tanjeffreyz/electrotactile-braille-display/images/oscilloscope_readings/IMG_0008.JPG

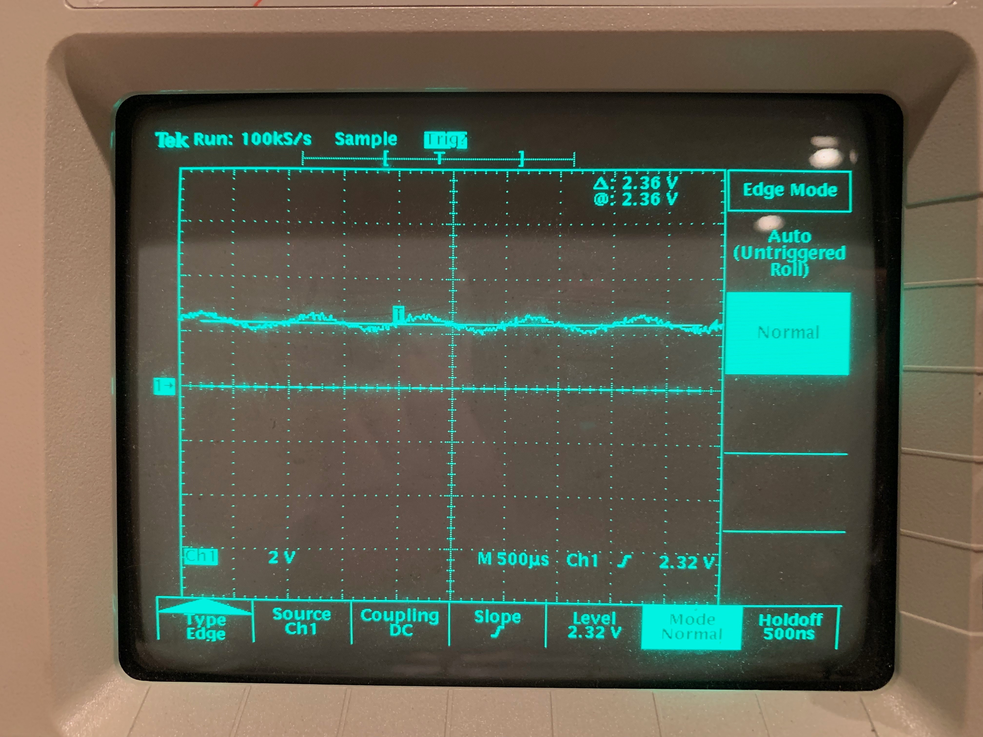
images/oscilloscope_readings/IMG_0008.JPG
