tanjeffreyz/electrotactile-braille-display/images/oscilloscope_readings/IMG_0009.JPG

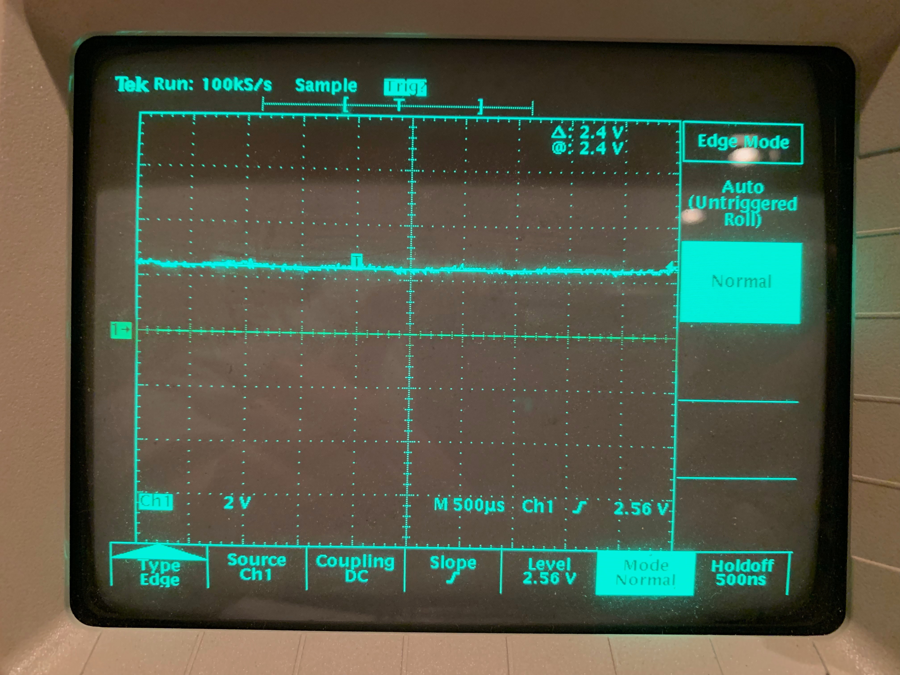
images/oscilloscope_readings/IMG_0009.JPG
