tanjeffreyz/electrotactile-braille-display/images/oscilloscope_readings/IMG_0010.JPG

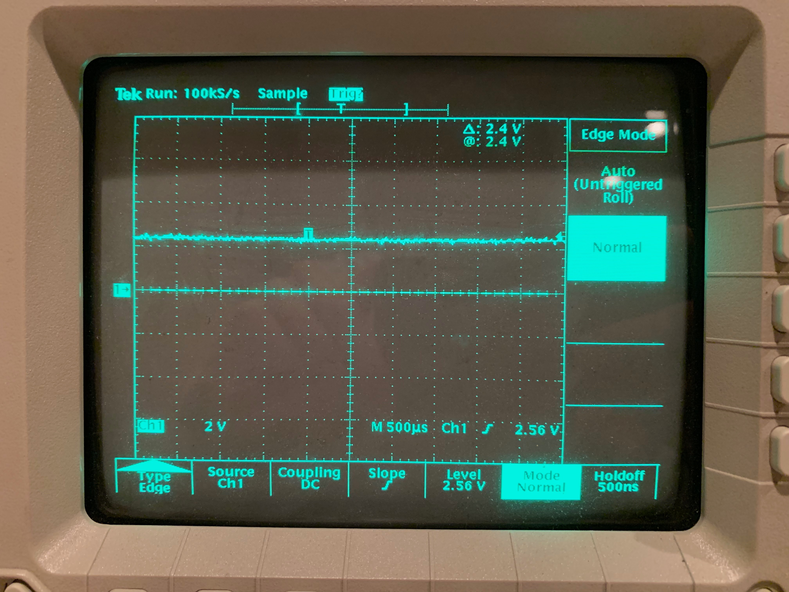
images/oscilloscope_readings/IMG_0010.JPG
