tanjeffreyz/electrotactile-braille-display/images/oscilloscope_readings/IMG_0014.JPG

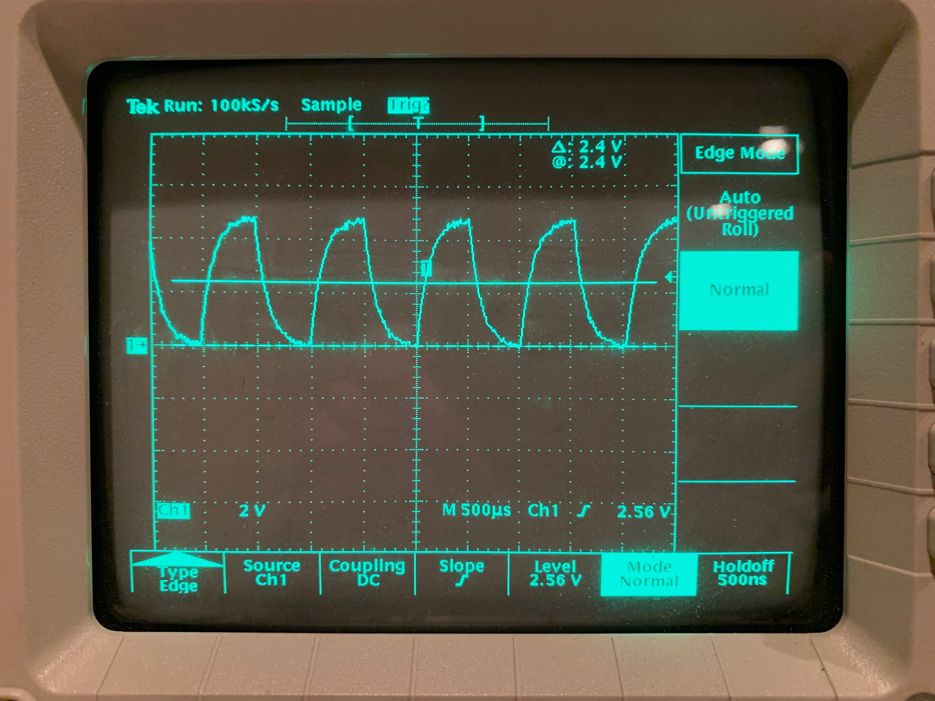
images/oscilloscope_readings/IMG_0014.JPG
