tanjeffreyz/electrotactile-braille-display/images/oscilloscope_readings/IMG_0118.JPG

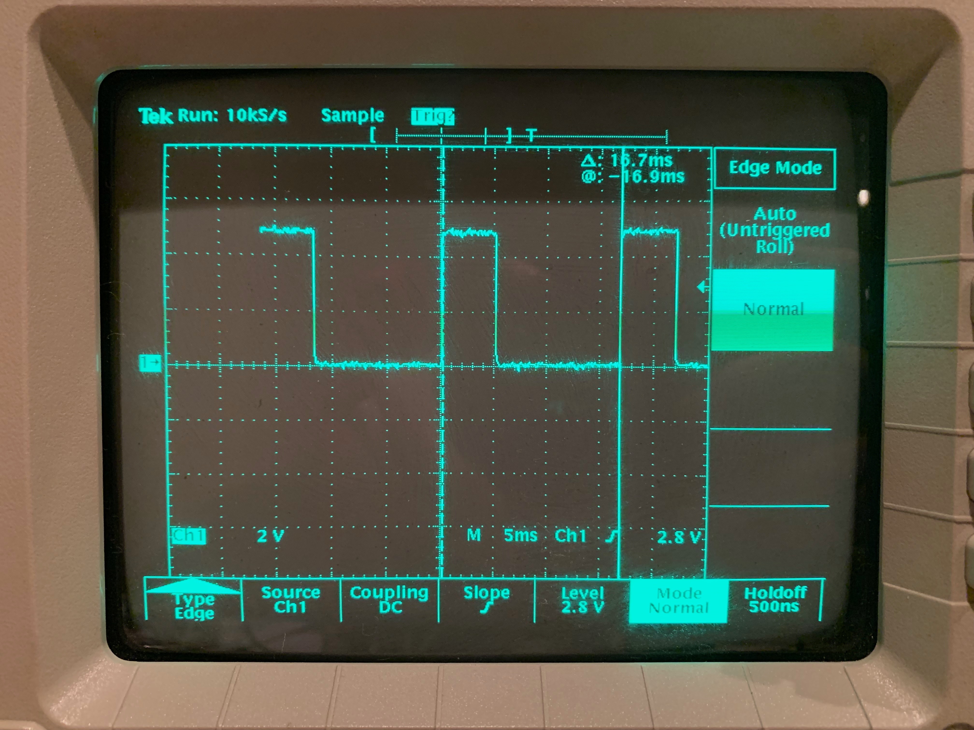
images/oscilloscope_readings/IMG_0118.JPG
