tanjeffreyz/electrotactile-braille-display/images/oscilloscope_readings/IMG_0120.JPG

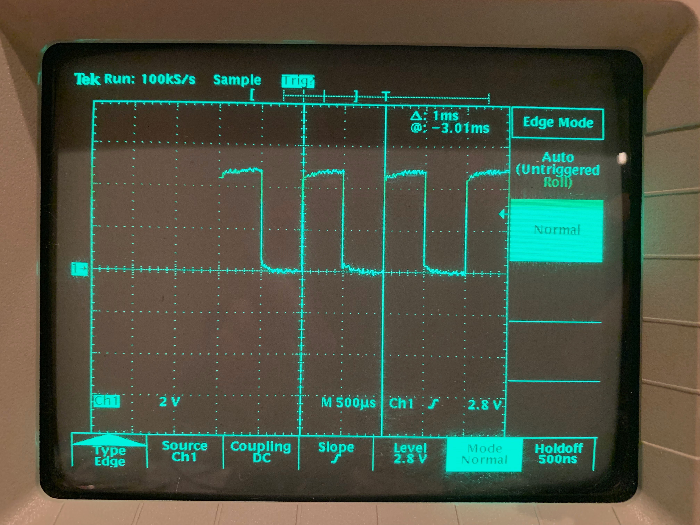
images/oscilloscope_readings/IMG_0120.JPG
