tanjeffreyz/electrotactile-braille-display/images/oscilloscope_readings/IMG_0123.JPG

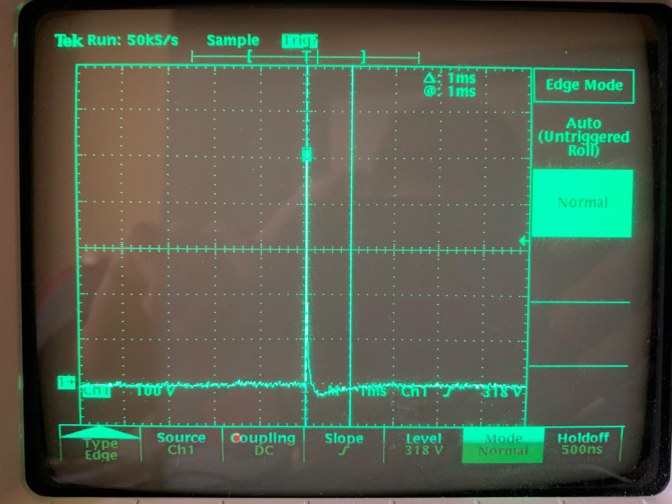
images/oscilloscope_readings/IMG_0123.JPG
