tanjeffreyz/electrotactile-braille-display/images/oscilloscope_readings/IMG_0124.JPG

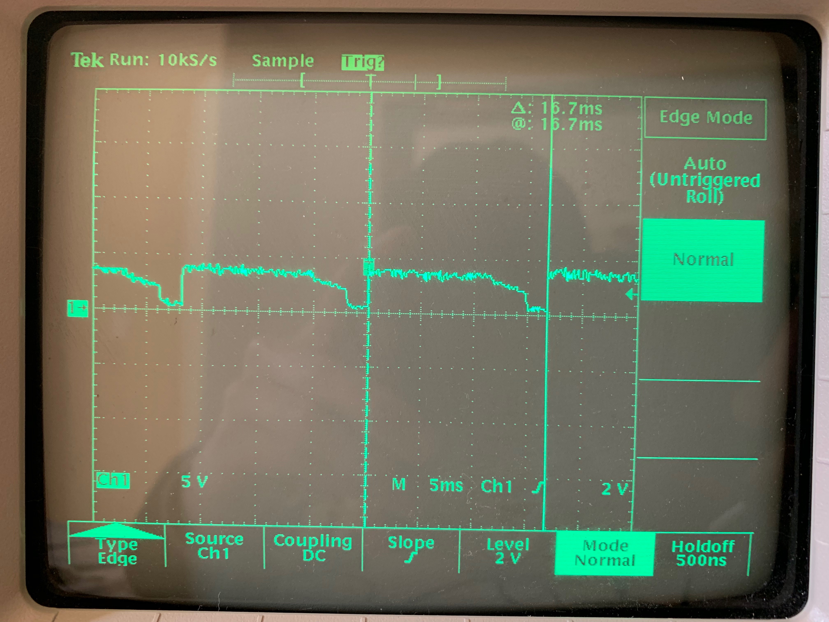
images/oscilloscope_readings/IMG_0124.JPG
