tanjeffreyz/electrotactile-braille-display/images/oscilloscope_readings/IMG_0125.JPG

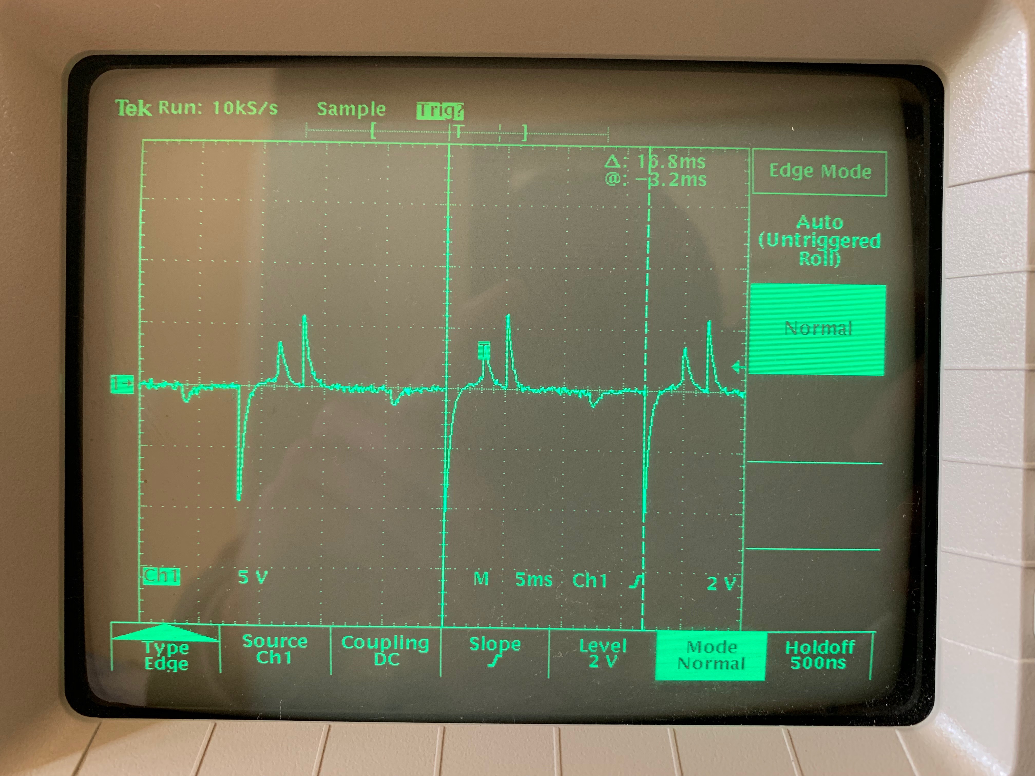
images/oscilloscope_readings/IMG_0125.JPG
