tanjeffreyz/electrotactile-braille-display/images/oscilloscope_readings/IMG_0386.JPG

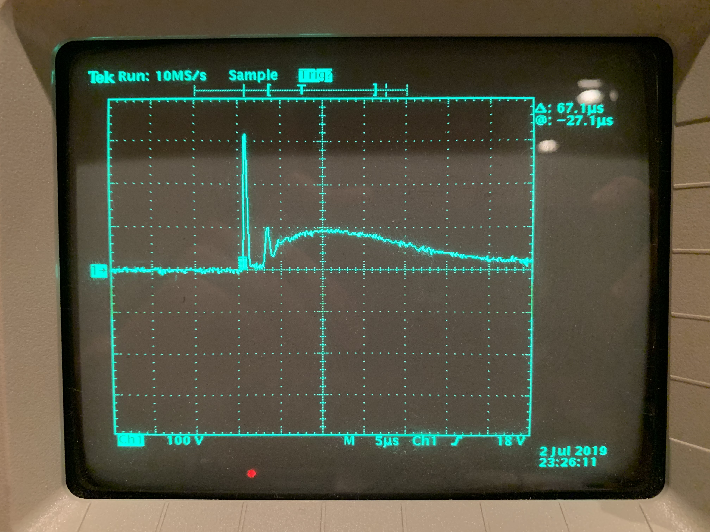
images/oscilloscope_readings/IMG_0386.JPG
