tanjeffreyz/electrotactile-braille-display/images/oscilloscope_readings/IMG_0387.JPG

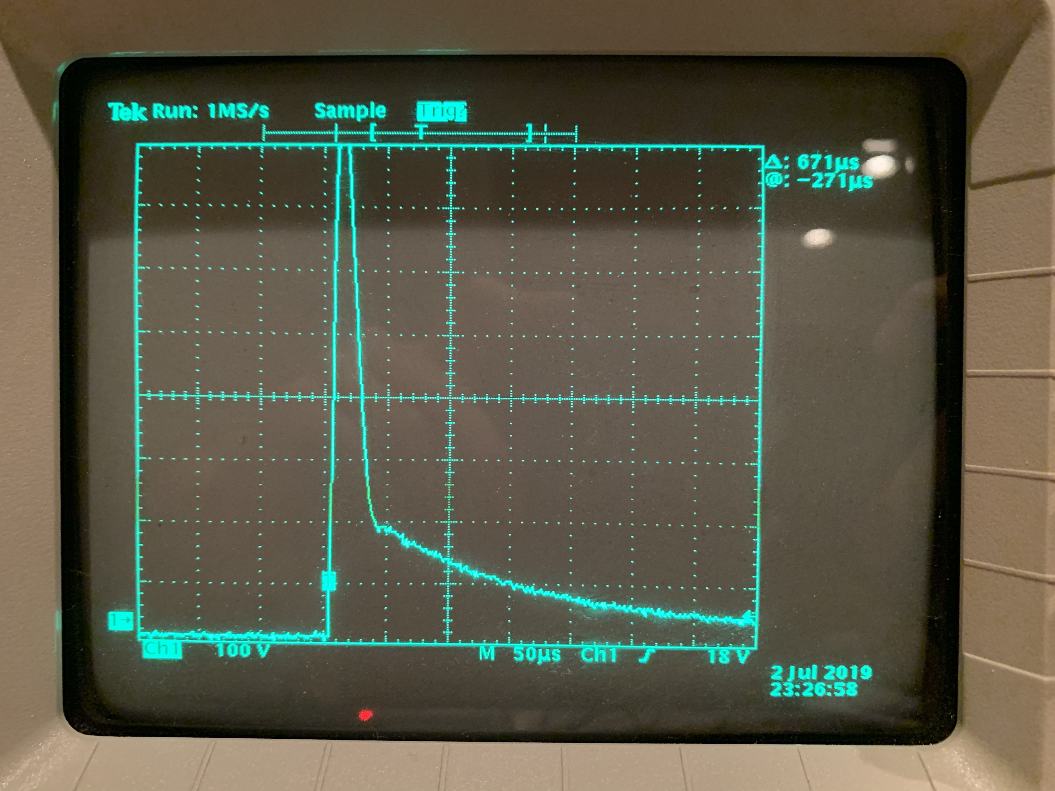
images/oscilloscope_readings/IMG_0387.JPG
