tanjeffreyz/electrotactile-braille-display/images/oscilloscope_readings/IMG_20190216_200049.jpg

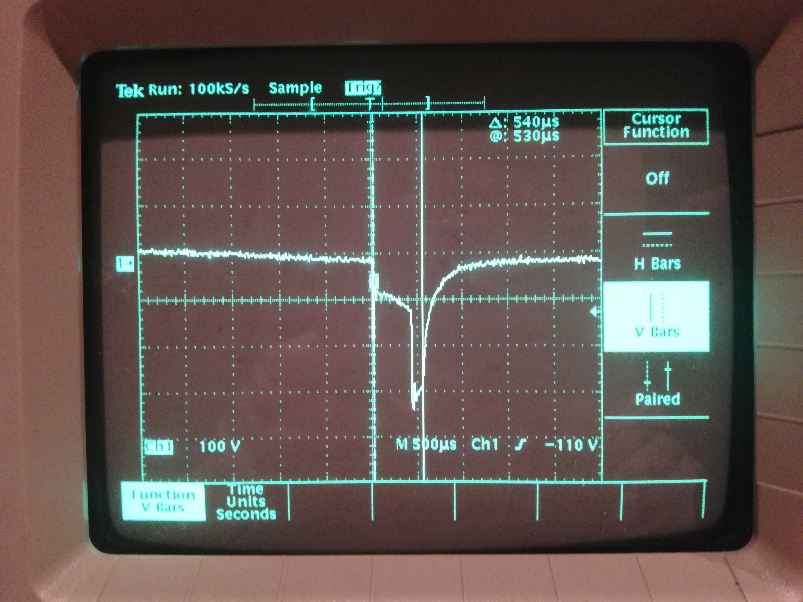
images/oscilloscope_readings/IMG_20190216_200049.jpg
