tanjeffreyz/electrotactile-braille-display/images/prototypes/IMG_0121.JPG

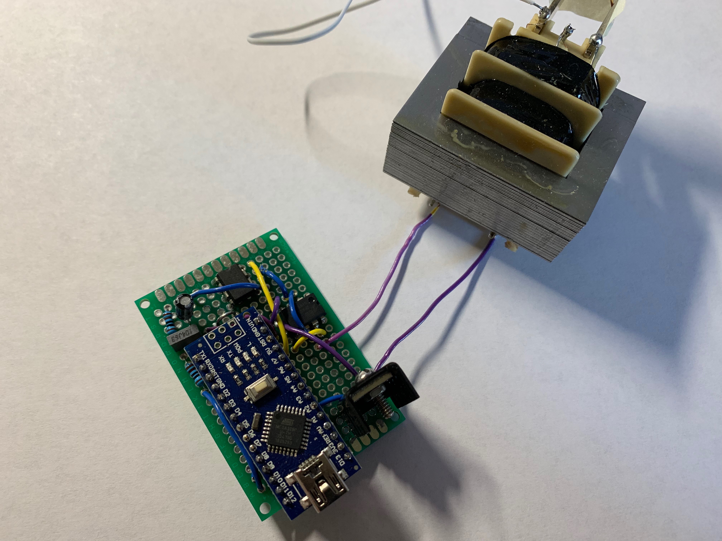
images/prototypes/IMG_0121.JPG
