tanjeffreyz/electrotactile-braille-display/images/prototypes/IMG_0122.JPG

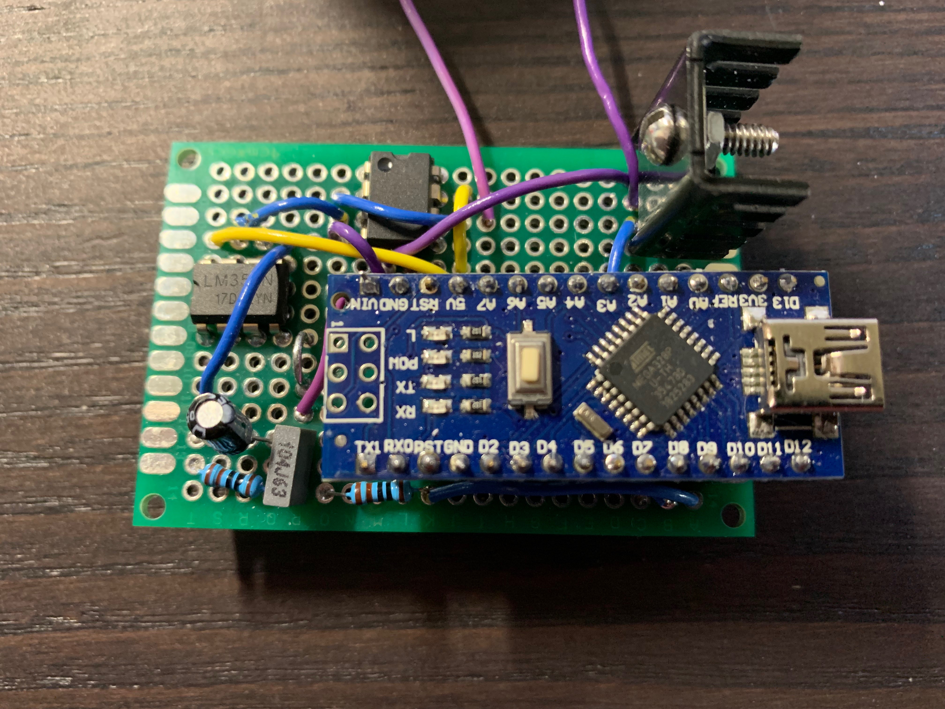
images/prototypes/IMG_0122.JPG
