tanjeffreyz/electrotactile-braille-display/images/prototypes/IMG_20190216_132523.jpg

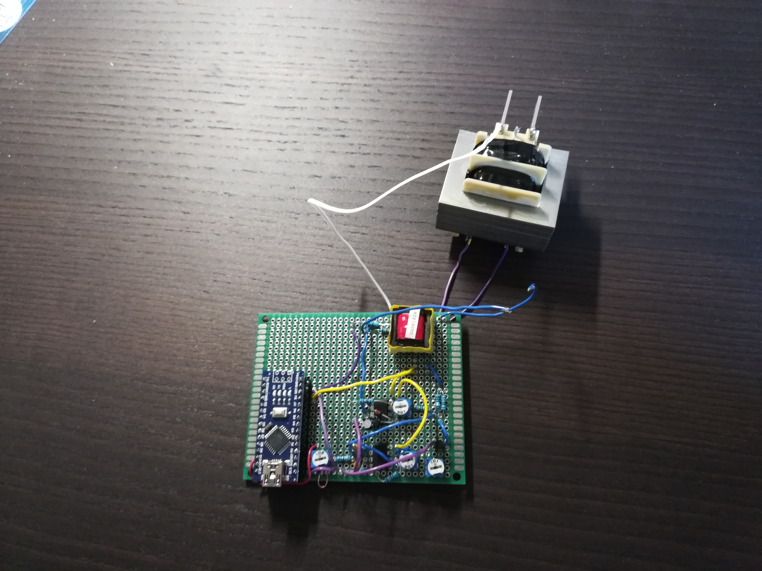
images/prototypes/IMG_20190216_132523.jpg
