tanjeffreyz/electrotactile-braille-display/images/prototypes/IMG_20190216_132549.jpg

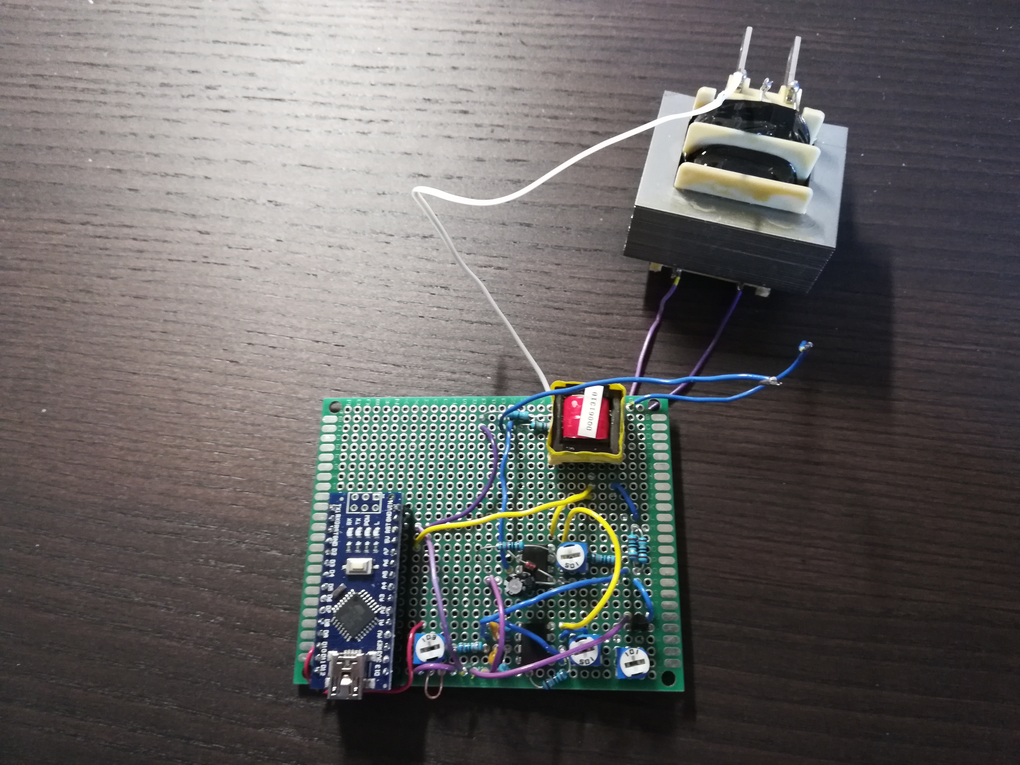
images/prototypes/IMG_20190216_132549.jpg
