tanjeffreyz/electrotactile-braille-display/images/prototypes/IMG_20190216_195744.jpg

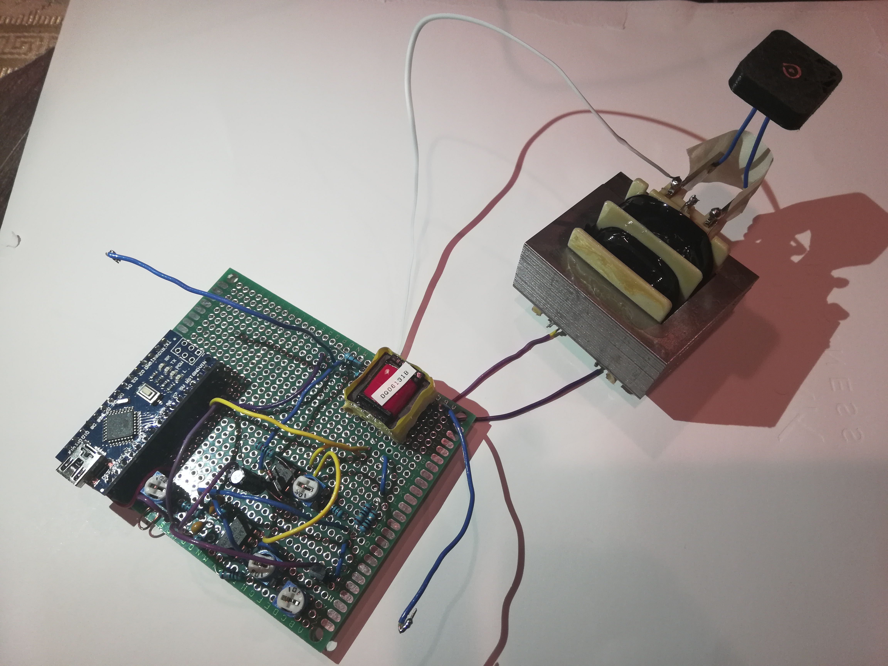
images/prototypes/IMG_20190216_195744.jpg
