tanjeffreyz/electrotactile-braille-display/images/prototypes/IMG_20190216_200214.jpg

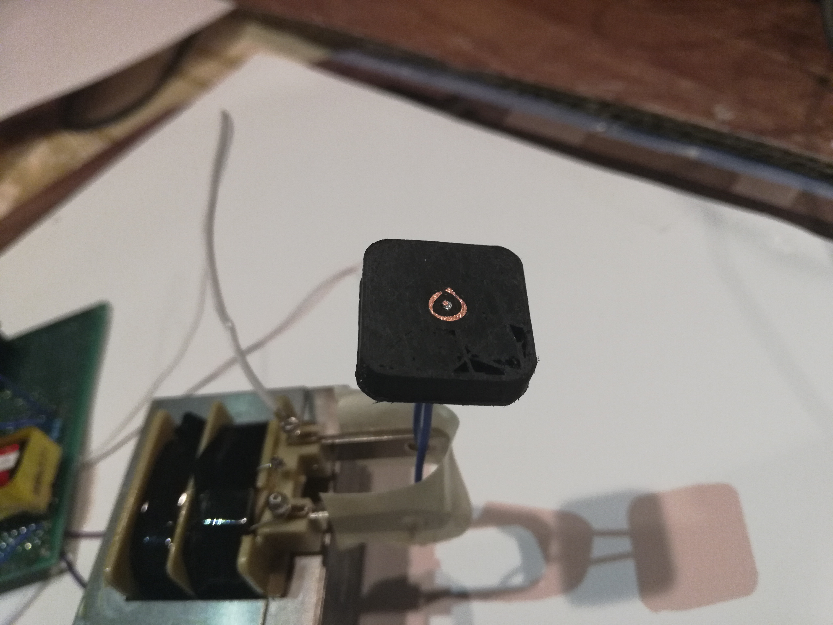
images/prototypes/IMG_20190216_200214.jpg
