tanjeffreyz/electrotactile-braille-display/images/schematics/Schematic v2.4.PNG

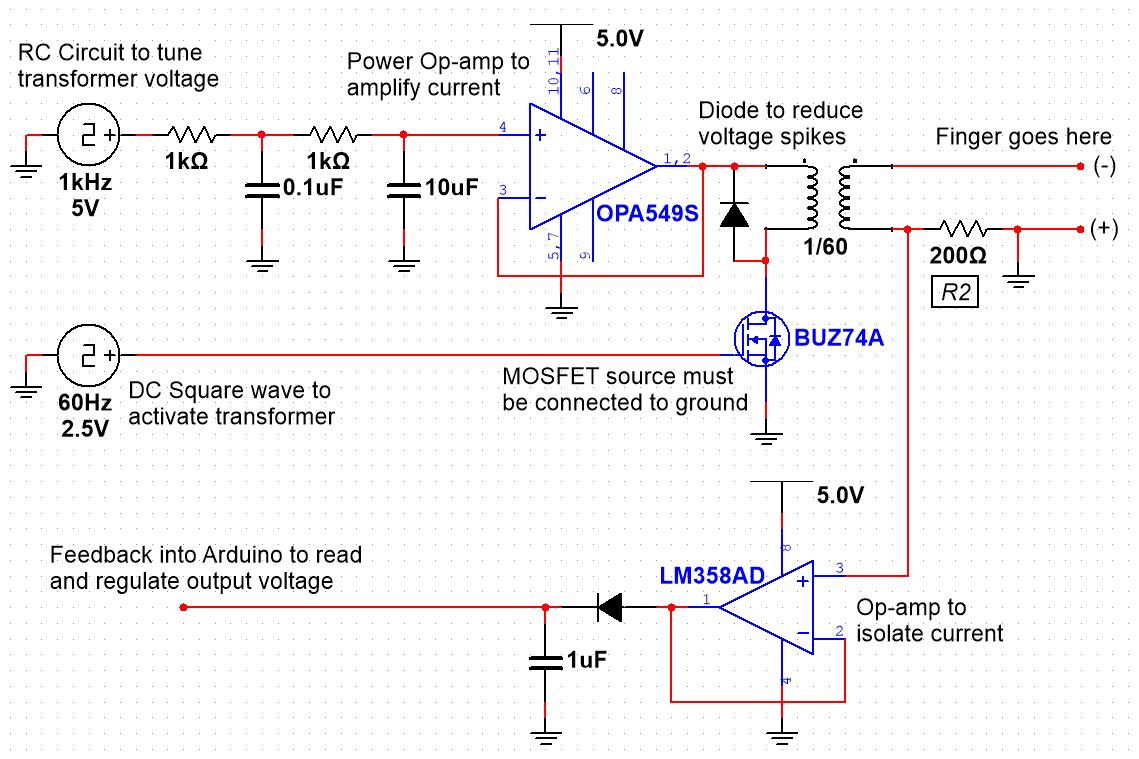
images/schematics/Schematic v2.4.PNG
