tanjeffreyz/electrotactile-braille-display/images/schematics/Schematic v2.6.png

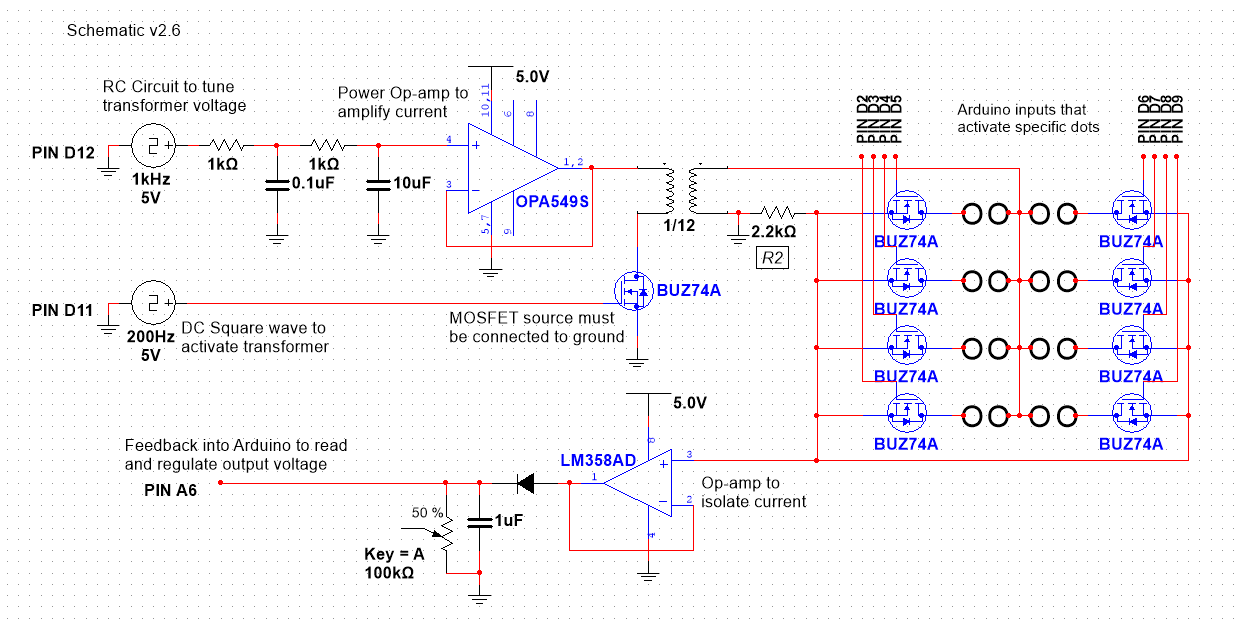
images/schematics/Schematic v2.6.png
