tanjeffreyz/electrotactile-braille-display/images/screenshots/Code v2.4.0 part1.PNG

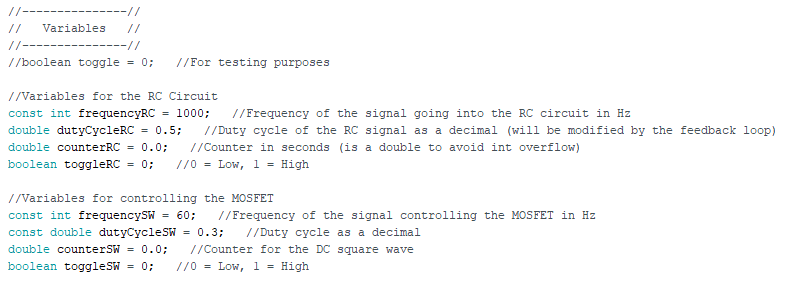
images/screenshots/Code v2.4.0 part1.PNG
