tanjeffreyz/electrotactile-braille-display/images/screenshots/Code v2.4.0 part3.PNG

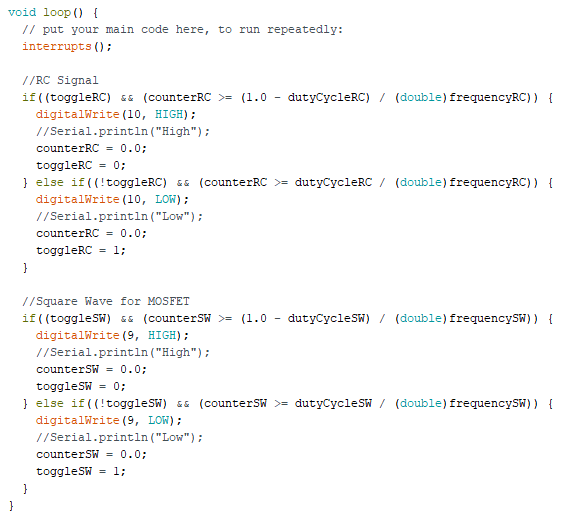
images/screenshots/Code v2.4.0 part3.PNG
