tanjeffreyz/electrotactile-braille-display/images/screenshots/dutyCycleRC Across Secondary Side Equation.PNG

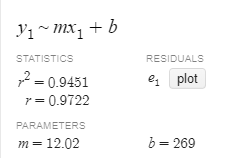
images/screenshots/dutyCycleRC Across Secondary Side Equation.PNG
