tanjeffreyz/electrotactile-braille-display/images/screenshots/dutyCycleRC Across Secondary Side Graph.PNG

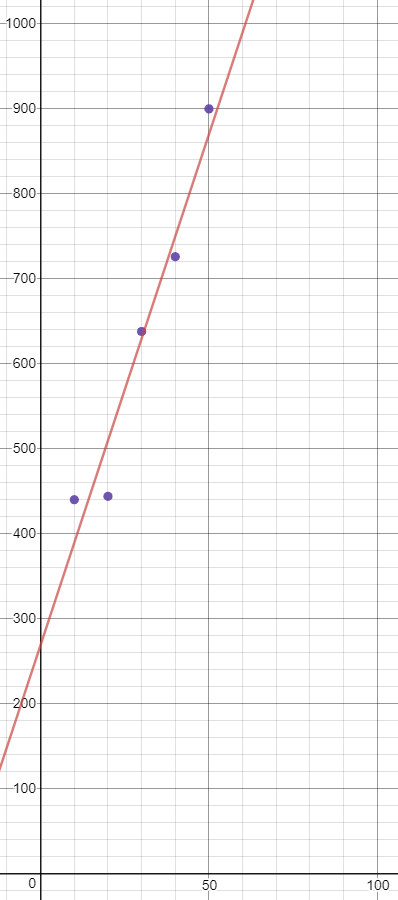
images/screenshots/dutyCycleRC Across Secondary Side Graph.PNG
