tanjeffreyz/electrotactile-braille-display/images/screenshots/dutyCycleRC Secondary to Ground Equation.PNG

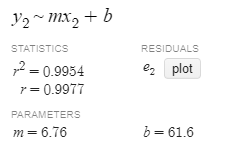
images/screenshots/dutyCycleRC Secondary to Ground Equation.PNG
