tanjeffreyz/electrotactile-braille-display/images/screenshots/dutyCycleRC Secondary to Ground Graph.PNG

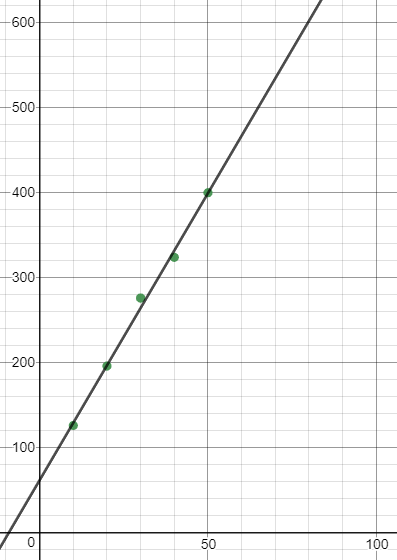
images/screenshots/dutyCycleRC Secondary to Ground Graph.PNG
