tanjeffreyz/electrotactile-braille-display/images/screenshots/Trial 1 Equation.PNG

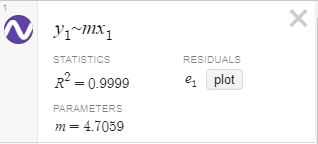
images/screenshots/Trial 1 Equation.PNG
