tanjeffreyz/electrotactile-braille-display/images/screenshots/Trial 1 Graph.PNG

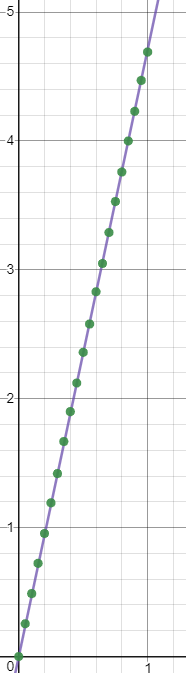
images/screenshots/Trial 1 Graph.PNG
