tanjeffreyz/electrotactile-braille-display/multisim/Optocouplers.jpg

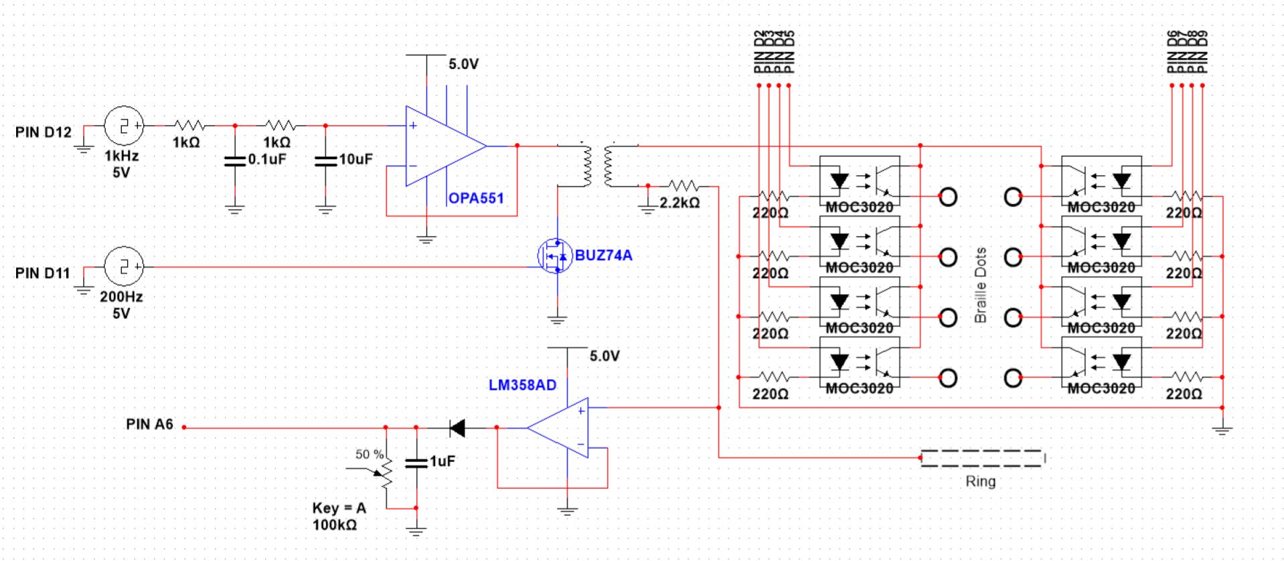
multisim/Optocouplers.jpg
